Han-ZenX/GPSDO/docs/references/carsten-andrich-gnssdo/GNSSDO主板_渲染_揭开OCXO罩_v2.jpg

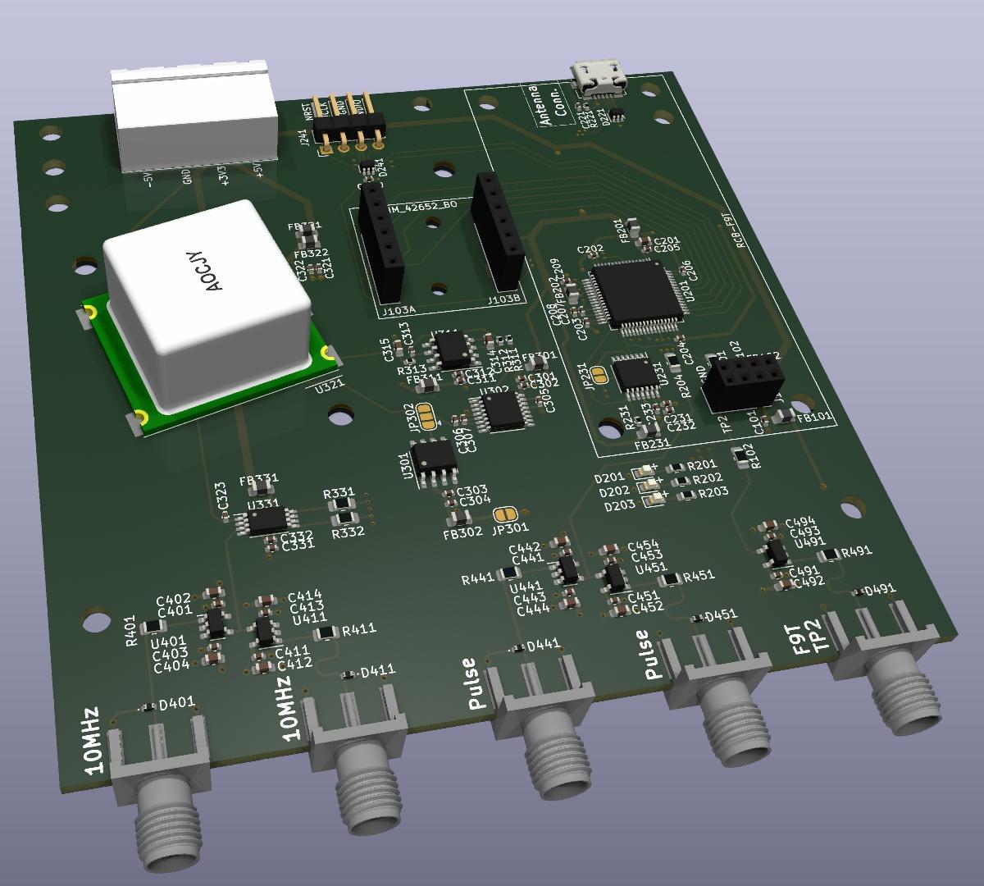
docs/references/carsten-andrich-gnssdo/GNSSDO主板_渲染_揭开OCXO罩_v2.jpg
