Han-ZenX/GPSDO/docs/references/carsten-andrich-gnssdo/GNSSDO主板_渲染_整板_v2.jpg

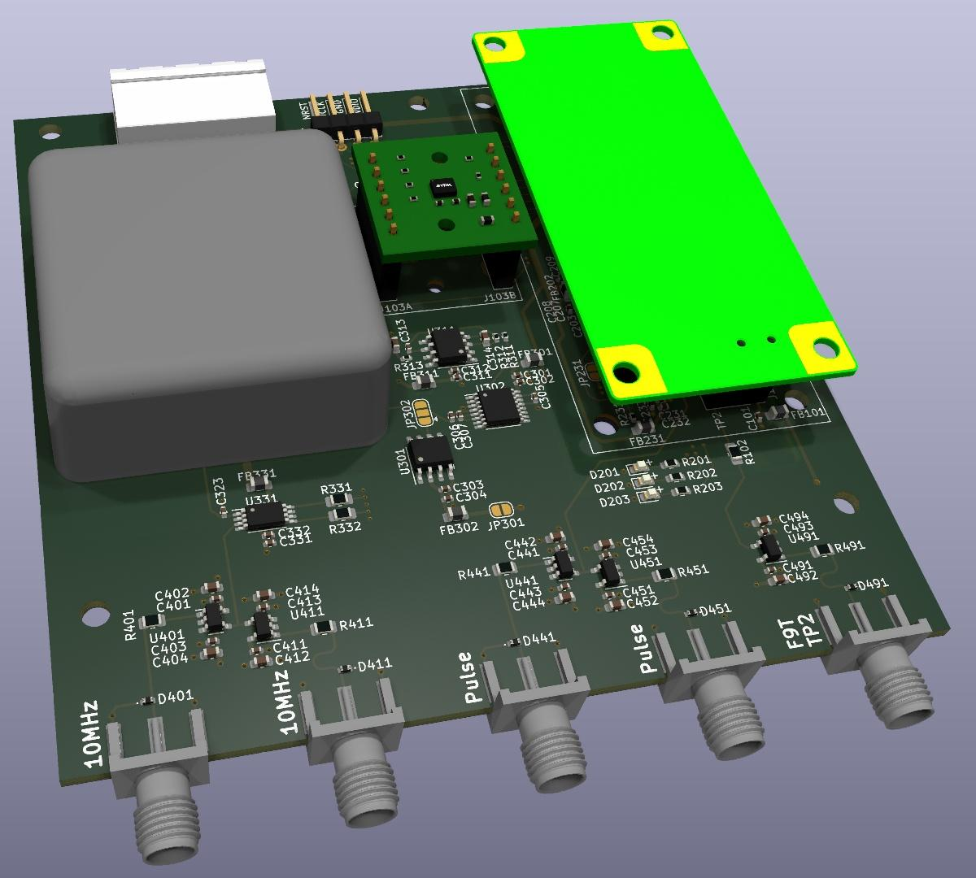
docs/references/carsten-andrich-gnssdo/GNSSDO主板_渲染_整板_v2.jpg
