Han-ZenX/GPSDO/docs/references/carsten-andrich-gnssdo/TDC7200测试板_实物_2022-08-28.jpg

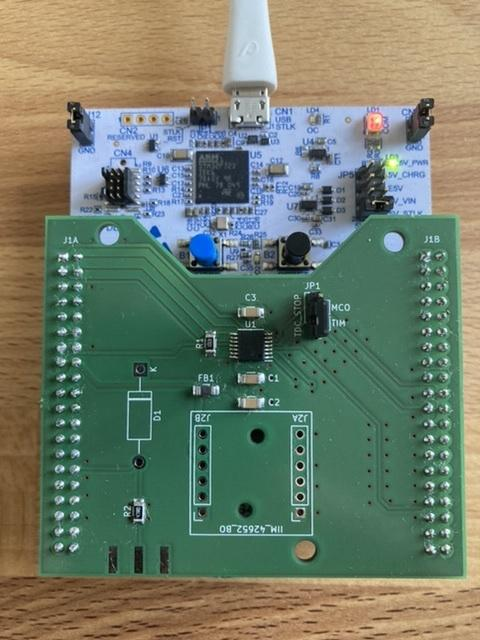
docs/references/carsten-andrich-gnssdo/TDC7200测试板_实物_2022-08-28.jpg
