Han-ZenX/GPSDO/hardware/schematic/v1.0/GPSDO_Rev1.0/GPSDO_Rev1.0.kicad_pcb

## KiCad design KiCad/steg_2.kicad_sch

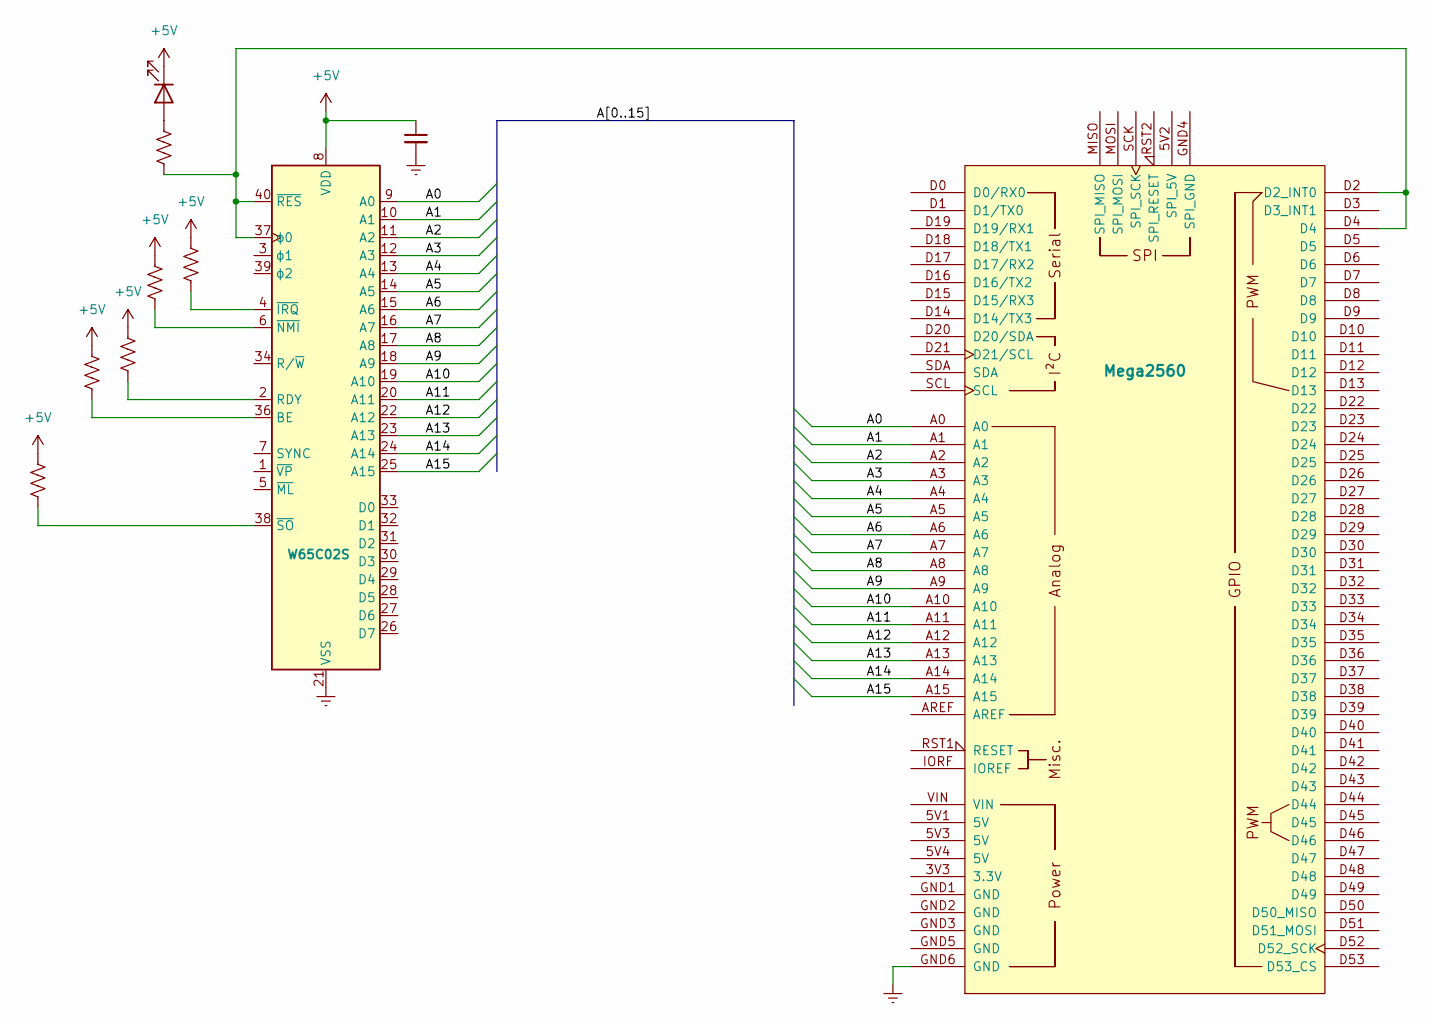
[picture p33: schematic steg_2.kicad_sch]

Parts:
A6: Mega2560; Arduino_Mega2560_R3_Shield
C2: 100nF
D2: LED
R29, R30, R31, R32, R33: (no value)
R34: 220
U12: W65C02S; DIP-40_W15.24mm

Connections:
+5V: C2.1, D2.1 (K), R29.1, R30.1, R31.1, R32.1, R33.1, U12.8 (VDD)
A0: A6.A0, U12.9 (A0)
A1: A6.A1, U12.10 (A1)
A2: A6.A2, U12.11 (A2)
A3: A6.A3, U12.12 (A3)
A4: A6.A4, U12.13 (A4)
A5: A6.A5, U12.14 (A5)
A6: A6.A6, U12.15 (A6)
A7: A6.A7, U12.16 (A7)
A8: A6.A8, U12.17 (A8)
A9: A6.A9, U12.18 (A9)
A10: A6.A10, U12.19 (A10)
A11: A6.A11, U12.20 (A11)
A12: A6.A12, U12.22 (A12)
A13: A6.A13, U12.23 (A13)
A14: A6.A14, U12.24 (A14)
A15: A6.A15, U12.25 (A15)
Earth: A6.GND6 (GND), C2.2, U12.21 (VSS)
unnamed: A6.D2 (D2_INT0), A6.D4, R34.2, U12.37 (ϕ0), U12.40 (~RES)
unnamed: D2.2 (A), R34.1
unnamed: R29.2, U12.38 (~SO)
unnamed: R30.2, U12.36 (BE)
unnamed: R31.2, U12.2 (RDY)
unnamed: R32.2, U12.6 (~NMI)
unnamed: R33.2, U12.4 (~IRQ)
