Han-ZenX/GPSDO/hardware/schematic/v1.0/GPSDO_Rev1.0/GPSDO_Rev1.0.kicad_pcb

## KiCad design KiCad/steg_4.kicad_sch

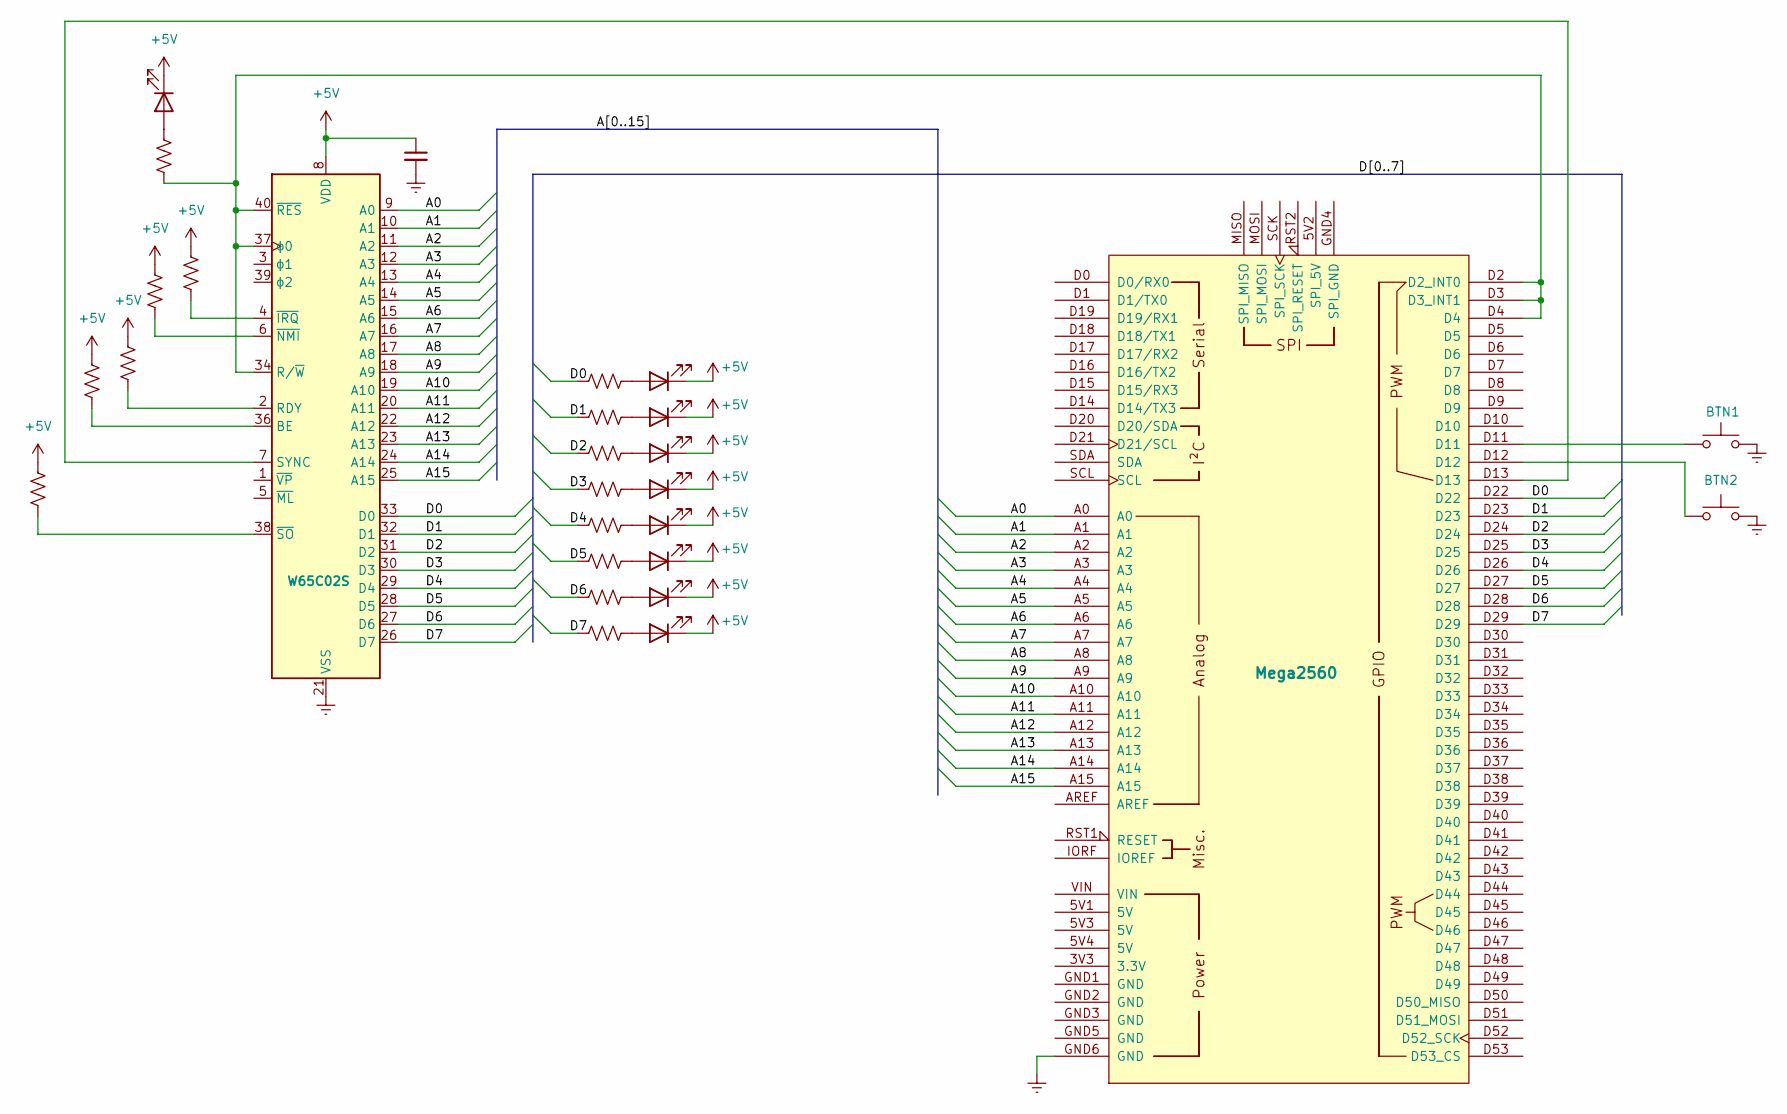
[picture p35: schematic steg_4.kicad_sch]

Parts:
A8: Mega2560; Arduino_Mega2560_R3_Shield
BTN1, BTN2: SW_Push
C4: 100nF
D12, D13, D14, D15, D16, D17, D18, D19, D20: LED
R49, R50, R51, R52, R54: (no value)
R53, R55, R56, R57, R58, R59, R60, R61, R62: 220
U14: W65C02S; DIP-40_W15.24mm

Connections:
+5V: C4.1, D12.1 (K), D13.1 (K), D14.1 (K), D15.1 (K), D16.1 (K), D17.1 (K), D18.1 (K), D19.1 (K), D20.1 (K), R49.1, R50.1, R51.1, R52.1, R54.1, U14.8 (VDD)
A0: A8.A0, U14.9 (A0)
A1: A8.A1, U14.10 (A1)
A2: A8.A2, U14.11 (A2)
A3: A8.A3, U14.12 (A3)
A4: A8.A4, U14.13 (A4)
A5: A8.A5, U14.14 (A5)
A6: A8.A6, U14.15 (A6)
A7: A8.A7, U14.16 (A7)
A8: A8.A8, U14.17 (A8)
A9: A8.A9, U14.18 (A9)
A10: A8.A10, U14.19 (A10)
A11: A8.A11, U14.20 (A11)
A12: A8.A12, U14.22 (A12)
A13: A8.A13, U14.23 (A13)
A14: A8.A14, U14.24 (A14)
A15: A8.A15, U14.25 (A15)
D0: A8.D22, R55.2, U14.33 (D0)
D1: A8.D23, R56.2, U14.32 (D1)
D2: A8.D24, R57.2, U14.31 (D2)
D3: A8.D25, R58.2, U14.30 (D3)
D4: A8.D26, R59.2, U14.29 (D4)
D5: A8.D27, R60.2, U14.28 (D5)
D6: A8.D28, R61.2, U14.27 (D6)
D7: A8.D29, R62.2, U14.26 (D7)
Earth: A8.GND6 (GND), BTN1.2, BTN2.2, C4.2, U14.21 (VSS)
unnamed: A8.D2 (D2_INT0), A8.D3 (D3_INT1), A8.D4, R53.2, U14.34 (R/~W), U14.37 (ϕ0), U14.40 (~RES)
unnamed: A8.D11, BTN1.1
unnamed: A8.D12, BTN2.1
unnamed: A8.D13, U14.7 (SYNC)
unnamed: D12.2 (A), R53.1
unnamed: D13.2 (A), R55.1
unnamed: D14.2 (A), R56.1
unnamed: D15.2 (A), R57.1
unnamed: D16.2 (A), R58.1
unnamed: D17.2 (A), R59.1
unnamed: D18.2 (A), R60.1
unnamed: D19.2 (A), R61.1
unnamed: D20.2 (A), R62.1
unnamed: R49.2, U14.38 (~SO)
unnamed: R50.2, U14.36 (BE)
unnamed: R51.2, U14.2 (RDY)
unnamed: R52.2, U14.6 (~NMI)
unnamed: R54.2, U14.4 (~IRQ)
