Han-ZenX/GPSDO/hardware/schematic/v1.0/GPSDO_Rev1.0/GPSDO_Rev1.0.kicad_pcb

## KiCad design KiCad/steg_5.kicad_sch

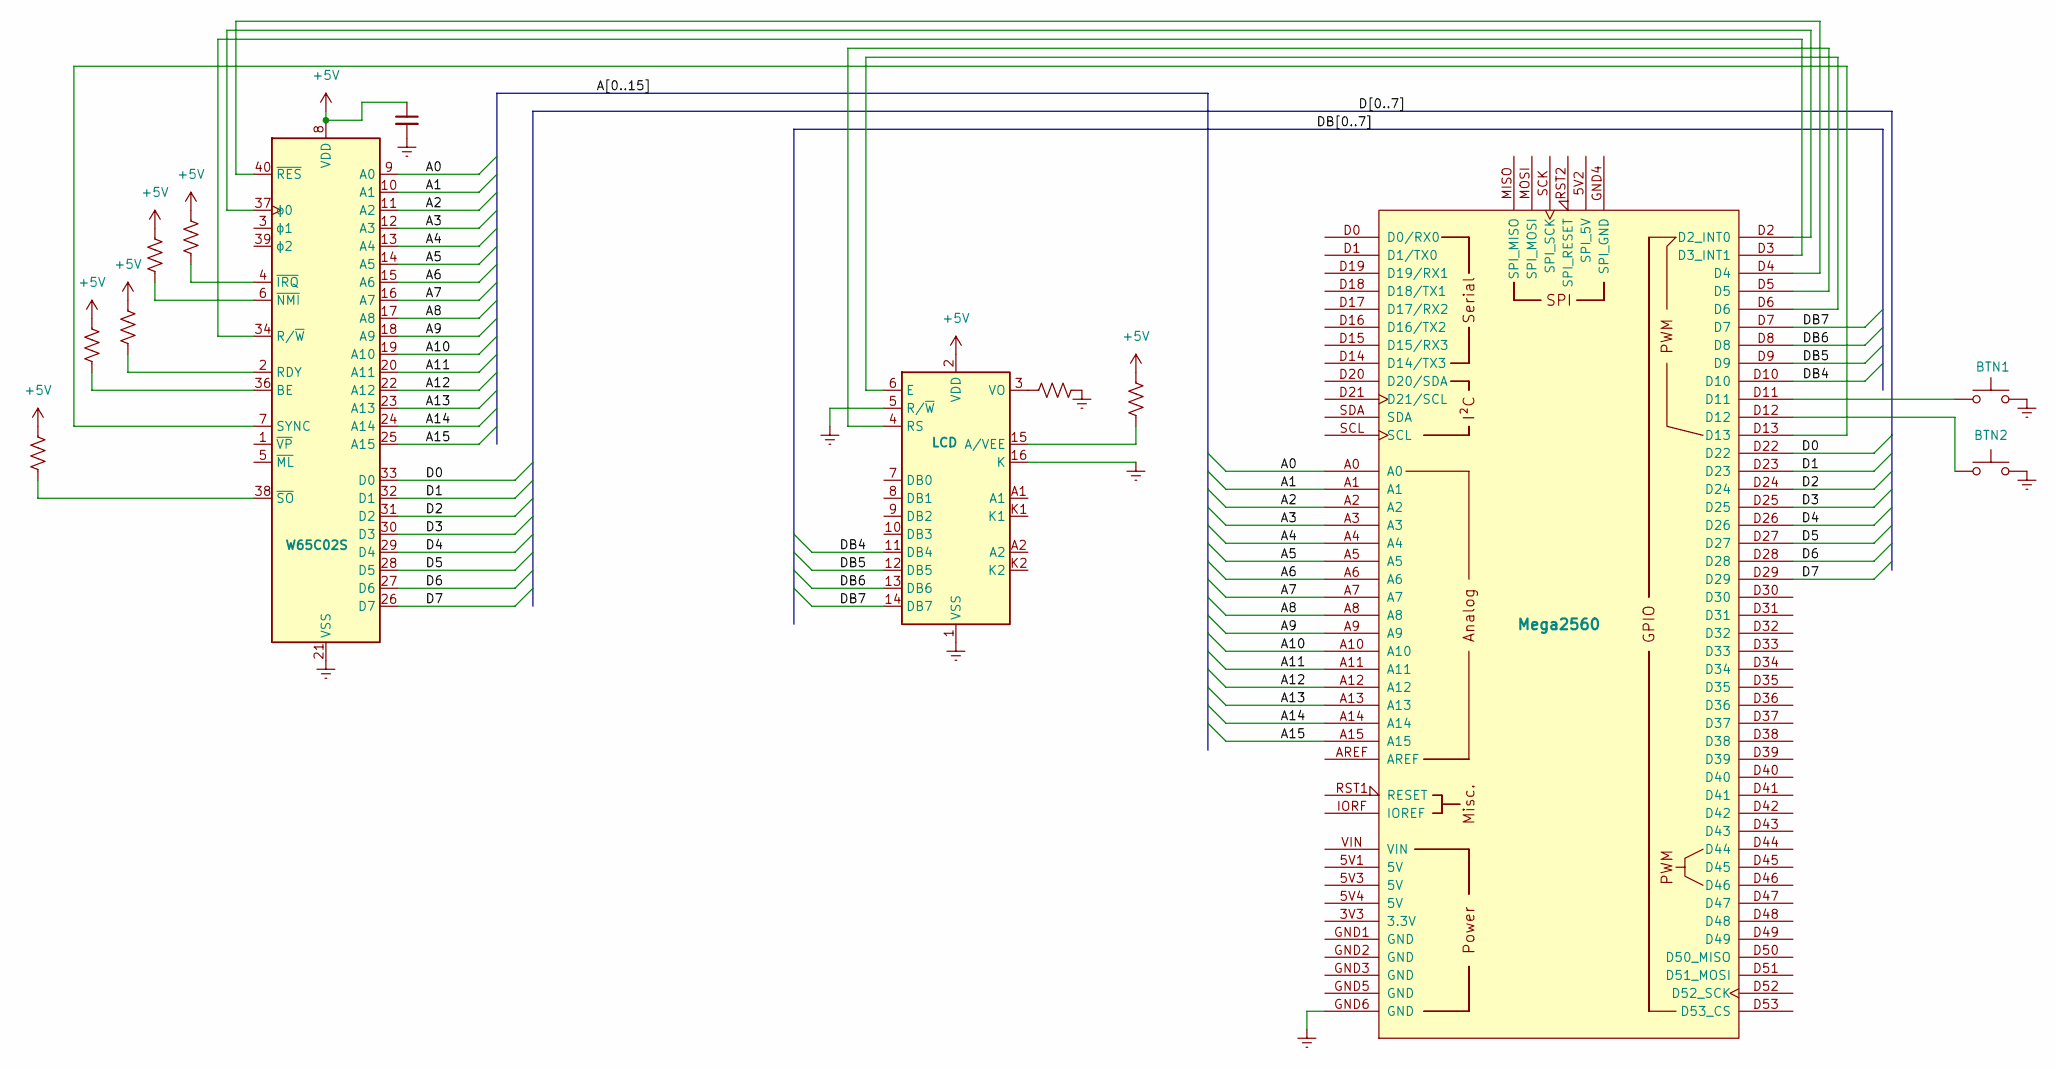
[picture p36: schematic steg_5.kicad_sch]

Parts:
A3: Mega2560; Arduino_Mega2560_R3_Shield
BTN1, BTN2: SW_Push
C5: 100nF
R15, R16, R17, R18, R19, R20, R21: (no value)
U7: W65C02S; DIP-40_W15.24mm
U8: LCD; LCD-016N002L

Connections:
+5V: C5.1, R15.1, R16.1, R17.1, R18.1, R19.1, R21.1, U7.8 (VDD), U8.2 (VDD)
A0: A3.A0, U7.9 (A0)
A1: A3.A1, U7.10 (A1)
A2: A3.A2, U7.11 (A2)
A3: A3.A3, U7.12 (A3)
A4: A3.A4, U7.13 (A4)
A5: A3.A5, U7.14 (A5)
A6: A3.A6, U7.15 (A6)
A7: A3.A7, U7.16 (A7)
A8: A3.A8, U7.17 (A8)
A9: A3.A9, U7.18 (A9)
A10: A3.A10, U7.19 (A10)
A11: A3.A11, U7.20 (A11)
A12: A3.A12, U7.22 (A12)
A13: A3.A13, U7.23 (A13)
A14: A3.A14, U7.24 (A14)
A15: A3.A15, U7.25 (A15)
D0: A3.D22, U7.33 (D0)
D1: A3.D23, U7.32 (D1)
D2: A3.D24, U7.31 (D2)
D3: A3.D25, U7.30 (D3)
D4: A3.D26, U7.29 (D4)
D5: A3.D27, U7.28 (D5)
D6: A3.D28, U7.27 (D6)
D7: A3.D29, U7.26 (D7)
DB4: A3.D10, U8.11 (DB4)
DB5: A3.D9, U8.12 (DB5)
DB6: A3.D8, U8.13 (DB6)
DB7: A3.D7, U8.14 (DB7)
Earth: A3.GND6 (GND), BTN1.2, BTN2.2, C5.2, R20.2, U7.21 (VSS), U8.1 (VSS), U8.5 (R/~W), U8.16 (K)
unnamed: A3.D2 (D2_INT0), U7.37 (ϕ0)
unnamed: A3.D3 (D3_INT1), U7.34 (R/~W)
unnamed: A3.D4, U7.40 (~RES)
unnamed: A3.D5, U8.4 (RS)
unnamed: A3.D6, U8.6 (E)
unnamed: A3.D11, BTN1.1
unnamed: A3.D12, BTN2.1
unnamed: A3.D13, U7.7 (SYNC)
unnamed: R15.2, U7.38 (~SO)
unnamed: R16.2, U7.36 (BE)
unnamed: R17.2, U7.2 (RDY)
unnamed: R18.2, U7.6 (~NMI)
unnamed: R19.2, U7.4 (~IRQ)
unnamed: R20.1, U8.3 (VO)
unnamed: R21.2, U8.15 (A/VEE)
