Han-ZenX/GPSDO/hardware/schematic/v1.0/GPSDO_Rev1.0/GPSDO_Rev1.0.kicad_pcb

## KiCad design KiCad/steg_6.kicad_sch

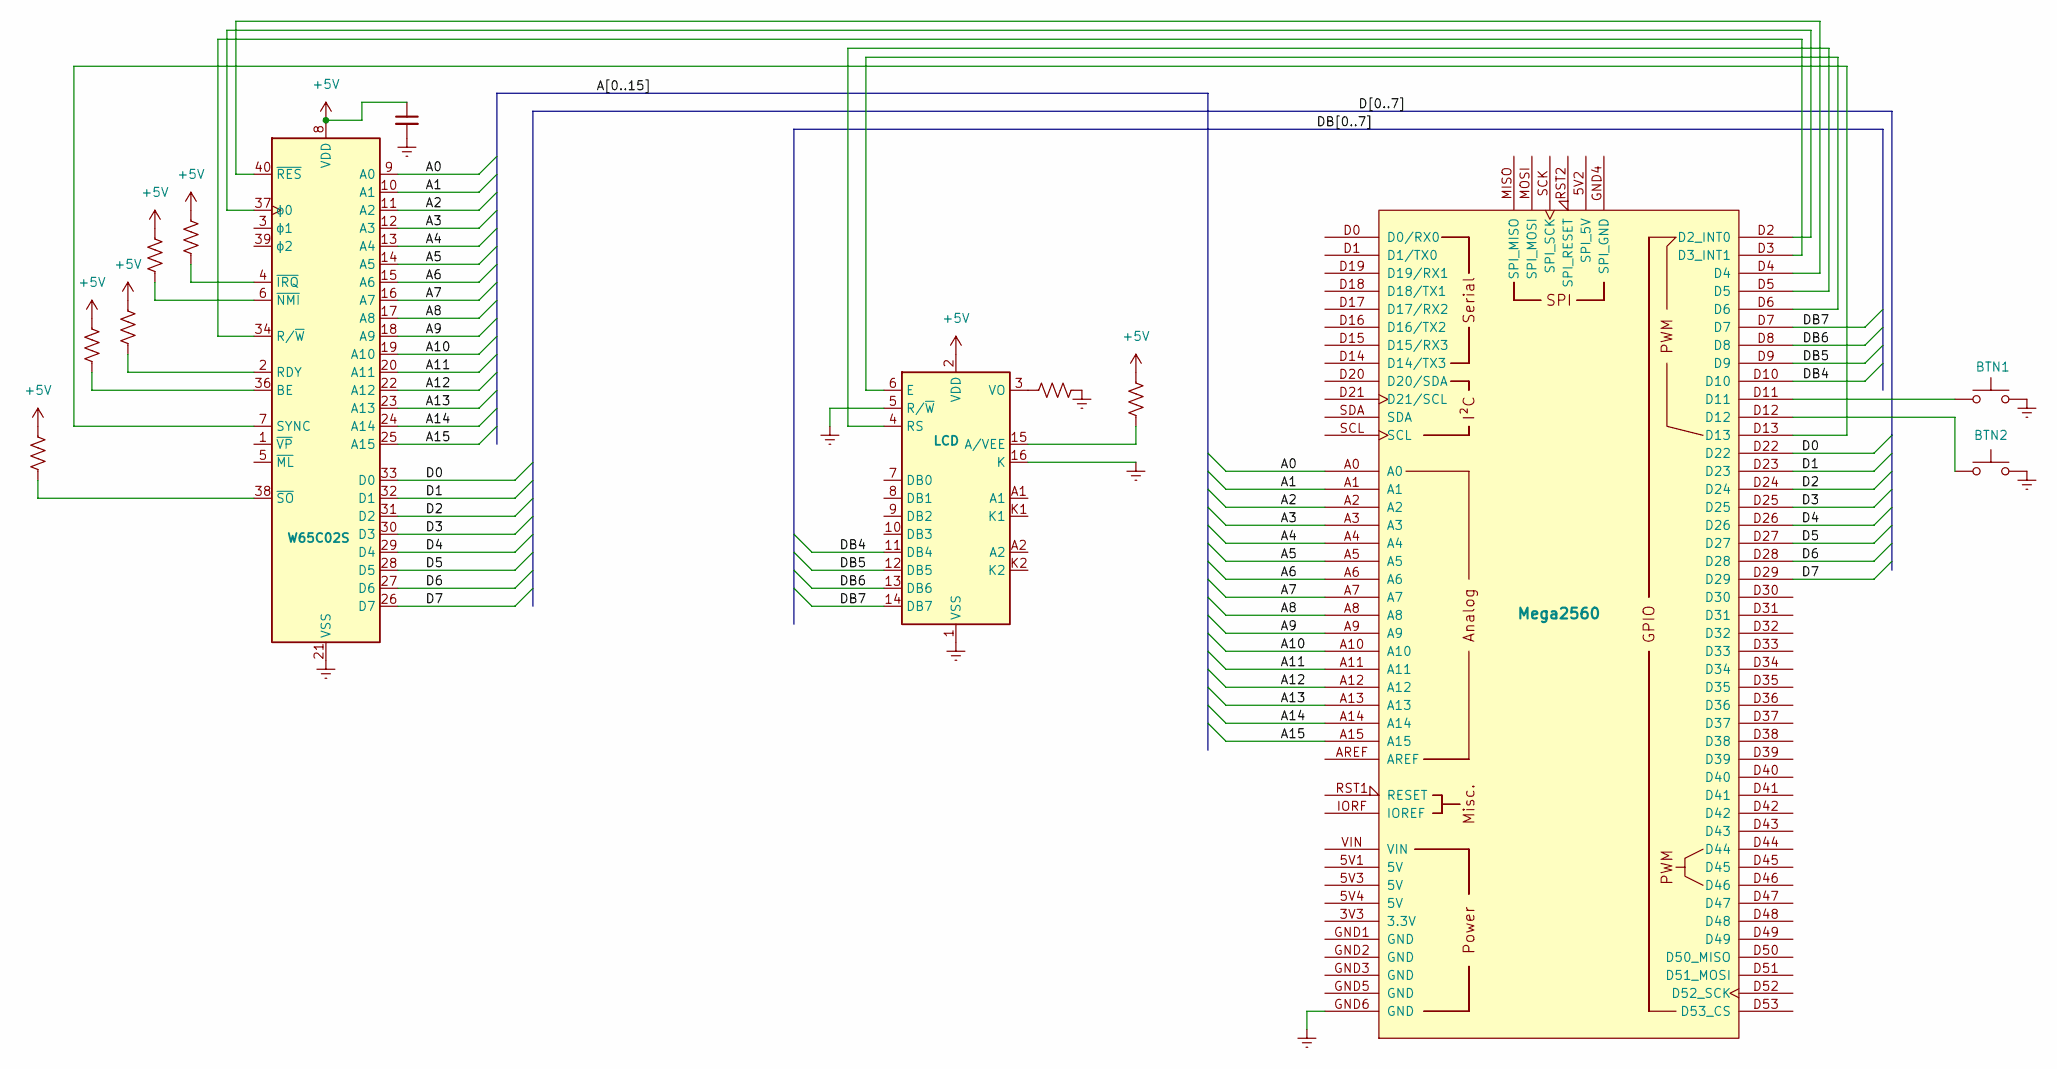
[picture p37: schematic steg_6.kicad_sch]

Parts:
A2: Mega2560; Arduino_Mega2560_R3_Shield
BTN1, BTN2: SW_Push
C6: 100nF
R8, R9, R10, R11, R12, R13, R14: (no value)
U5: W65C02S; DIP-40_W15.24mm
U6: LCD; LCD-016N002L

Connections:
+5V: C6.1, R8.1, R9.1, R10.1, R11.1, R12.1, R14.1, U5.8 (VDD), U6.2 (VDD)
A0: A2.A0, U5.9 (A0)
A1: A2.A1, U5.10 (A1)
A2: A2.A2, U5.11 (A2)
A3: A2.A3, U5.12 (A3)
A4: A2.A4, U5.13 (A4)
A5: A2.A5, U5.14 (A5)
A6: A2.A6, U5.15 (A6)
A7: A2.A7, U5.16 (A7)
A8: A2.A8, U5.17 (A8)
A9: A2.A9, U5.18 (A9)
A10: A2.A10, U5.19 (A10)
A11: A2.A11, U5.20 (A11)
A12: A2.A12, U5.22 (A12)
A13: A2.A13, U5.23 (A13)
A14: A2.A14, U5.24 (A14)
A15: A2.A15, U5.25 (A15)
D0: A2.D22, U5.33 (D0)
D1: A2.D23, U5.32 (D1)
D2: A2.D24, U5.31 (D2)
D3: A2.D25, U5.30 (D3)
D4: A2.D26, U5.29 (D4)
D5: A2.D27, U5.28 (D5)
D6: A2.D28, U5.27 (D6)
D7: A2.D29, U5.26 (D7)
DB4: A2.D10, U6.11 (DB4)
DB5: A2.D9, U6.12 (DB5)
DB6: A2.D8, U6.13 (DB6)
DB7: A2.D7, U6.14 (DB7)
Earth: A2.GND6 (GND), BTN1.2, BTN2.2, C6.2, R13.2, U5.21 (VSS), U6.1 (VSS), U6.5 (R/~W), U6.16 (K)
unnamed: A2.D2 (D2_INT0), U5.37 (ϕ0)
unnamed: A2.D3 (D3_INT1), U5.34 (R/~W)
unnamed: A2.D4, U5.40 (~RES)
unnamed: A2.D5, U6.4 (RS)
unnamed: A2.D6, U6.6 (E)
unnamed: A2.D11, BTN1.1
unnamed: A2.D12, BTN2.1
unnamed: A2.D13, U5.7 (SYNC)
unnamed: R8.2, U5.38 (~SO)
unnamed: R9.2, U5.36 (BE)
unnamed: R10.2, U5.2 (RDY)
unnamed: R11.2, U5.6 (~NMI)
unnamed: R12.2, U5.4 (~IRQ)
unnamed: R13.1, U6.3 (VO)
unnamed: R14.2, U6.15 (A/VEE)
