Han-ZenX/GPSDO/hardware/schematic/v1.0/GPSDO_Rev1.0/GPSDO_Rev1.0.kicad_pcb

## KiCad design KiCad/steg_11.kicad_sch

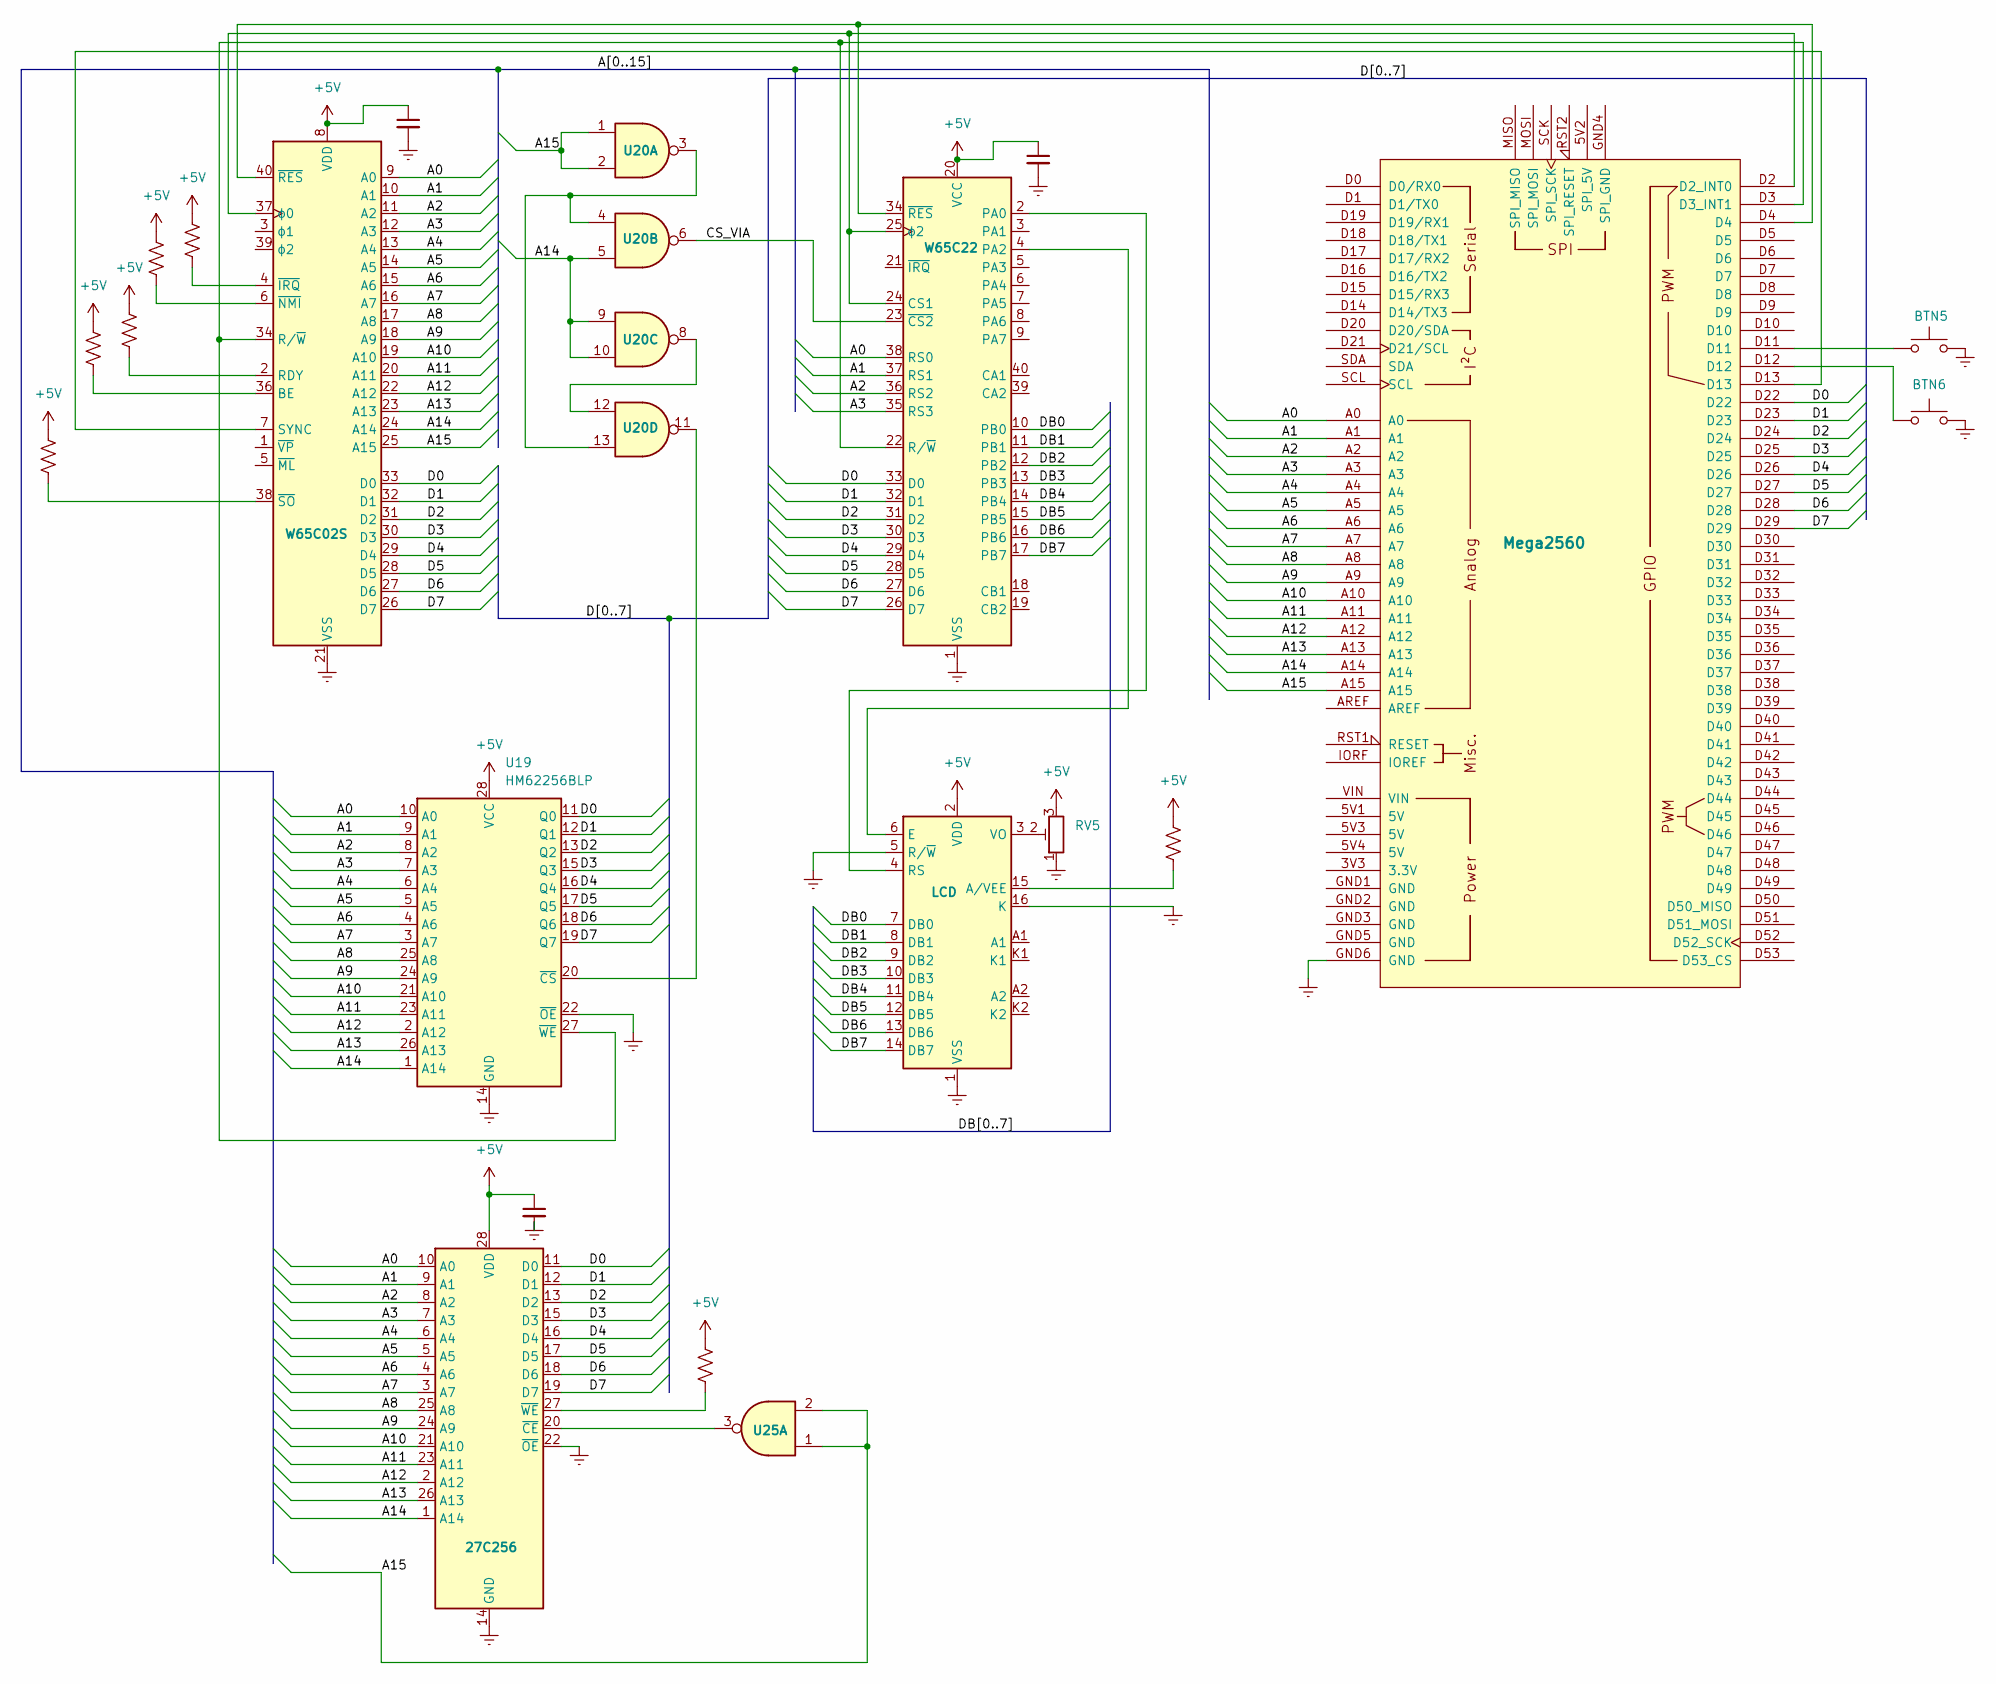
[picture p41: schematic steg_11.kicad_sch]

Parts:
A10: Mega2560; Arduino_Mega2560_R3_Shield
BTN5, BTN6: SW_Push
C12, C13, C14: 100nF
R25, R26, R27, R28, R63, R65: (no value)
R64: 220
RV5: R_Potentiometer_Trim
U18: W65C02S; DIP-40_W15.24mm
U19: HM62256BLP; DIP-28_W15.24mm
U20, U25: 74HC00
U21: W65C22; DIP-40_W15.24mm
U22: LCD; LCD-016N002L
U23: 27C256; DIP-28_W15.24mm

Connections:
+5V: C12.1, C13.1, C14.1, R25.1, R26.1, R27.1, R28.1, R63.1, R64.1, R65.1, RV5.3, U18.8 (VDD), U19.28 (VCC), U21.20 (VCC), U22.2 (VDD), U23.28 (VDD)
A0: A10.A0, U18.9 (A0), U19.10 (A0), U21.38 (RS0), U23.10 (A0)
A1: A10.A1, U18.10 (A1), U19.9 (A1), U21.37 (RS1), U23.9 (A1)
A2: A10.A2, U18.11 (A2), U19.8 (A2), U21.36 (RS2), U23.8 (A2)
A3: A10.A3, U18.12 (A3), U19.7 (A3), U21.35 (RS3), U23.7 (A3)
A4: A10.A4, U18.13 (A4), U19.6 (A4), U23.6 (A4)
A5: A10.A5, U18.14 (A5), U19.5 (A5), U23.5 (A5)
A6: A10.A6, U18.15 (A6), U19.4 (A6), U23.4 (A6)
A7: A10.A7, U18.16 (A7), U19.3 (A7), U23.3 (A7)
A8: A10.A8, U18.17 (A8), U19.25 (A8), U23.25 (A8)
A9: A10.A9, U18.18 (A9), U19.24 (A9), U23.24 (A9)
A10: A10.A10, U18.19 (A10), U19.21 (A10), U23.21 (A10)
A11: A10.A11, U18.20 (A11), U19.23 (A11), U23.23 (A11)
A12: A10.A12, U18.22 (A12), U19.2 (A12), U23.2 (A12)
A13: A10.A13, U18.23 (A13), U19.26 (A13), U23.26 (A13)
A14: A10.A14, U18.24 (A14), U19.1 (A14), U20.5, U20.9, U20.10, U23.1 (A14)
A15: A10.A15, U18.25 (A15), U20.1, U20.2, U25.1, U25.2
CS_VIA: U20.6, U21.23 (~CS2)
D0: A10.D22, U18.33 (D0), U19.11 (Q0), U21.33 (D0), U23.11 (D0)
D1: A10.D23, U18.32 (D1), U19.12 (Q1), U21.32 (D1), U23.12 (D1)
D2: A10.D24, U18.31 (D2), U19.13 (Q2), U21.31 (D2), U23.13 (D2)
D3: A10.D25, U18.30 (D3), U19.15 (Q3), U21.30 (D3), U23.15 (D3)
D4: A10.D26, U18.29 (D4), U19.16 (Q4), U21.29 (D4), U23.16 (D4)
D5: A10.D27, U18.28 (D5), U19.17 (Q5), U21.28 (D5), U23.17 (D5)
D6: A10.D28, U18.27 (D6), U19.18 (Q6), U21.27 (D6), U23.18 (D6)
D7: A10.D29, U18.26 (D7), U19.19 (Q7), U21.26 (D7), U23.19 (D7)
DB0: U21.10 (PB0), U22.7 (DB0)
DB1: U21.11 (PB1), U22.8 (DB1)
DB2: U21.12 (PB2), U22.9 (DB2)
DB3: U21.13 (PB3), U22.10 (DB3)
DB4: U21.14 (PB4), U22.11 (DB4)
DB5: U21.15 (PB5), U22.12 (DB5)
DB6: U21.16 (PB6), U22.13 (DB6)
DB7: U21.17 (PB7), U22.14 (DB7)
Earth: A10.GND6 (GND), BTN5.2, BTN6.2, C12.2, C13.2, C14.2, RV5.1, U18.21 (VSS), U19.14 (GND), U19.22 (~OE), U21.1 (VSS), U22.1 (VSS), U22.5 (R/~W), U22.16 (K), U23.14 (GND), U23.22 (~OE)
unnamed: A10.D2 (D2_INT0), U18.37 (ϕ0), U21.24 (CS1), U21.25 (ϕ2)
unnamed: A10.D3 (D3_INT1), U18.34 (R/~W), U19.27 (~WE), U21.22 (R/~W)
unnamed: A10.D4, U18.40 (~RES), U21.34 (~RES)
unnamed: A10.D11, BTN5.1
unnamed: A10.D12, BTN6.1
unnamed: A10.D13, U18.7 (SYNC)
unnamed: R25.2, U18.38 (~SO)
unnamed: R26.2, U18.36 (BE)
unnamed: R27.2, U18.2 (RDY)
unnamed: R28.2, U18.6 (~NMI)
unnamed: R63.2, U18.4 (~IRQ)
unnamed: R64.2, U22.15 (A/VEE)
unnamed: R65.2, U23.27 (~WE)
unnamed: RV5.2, U22.3 (VO)
unnamed: U19.20 (~CS), U20.11
unnamed: U20.8, U20.12
unnamed: U20.3, U20.4, U20.13
unnamed: U21.2 (PA0), U22.4 (RS)
unnamed: U21.4 (PA2), U22.6 (E)
unnamed: U23.20 (~CE), U25.3
