Han-ZenX/GPSDO/hardware/schematic/v1.0/GPSDO_Rev1.0/GPSDO_Rev1.0.kicad_pcb

## KiCad design KiCad/6502.smutje.se.steg-6/6502.smutje.se.kicad_sch

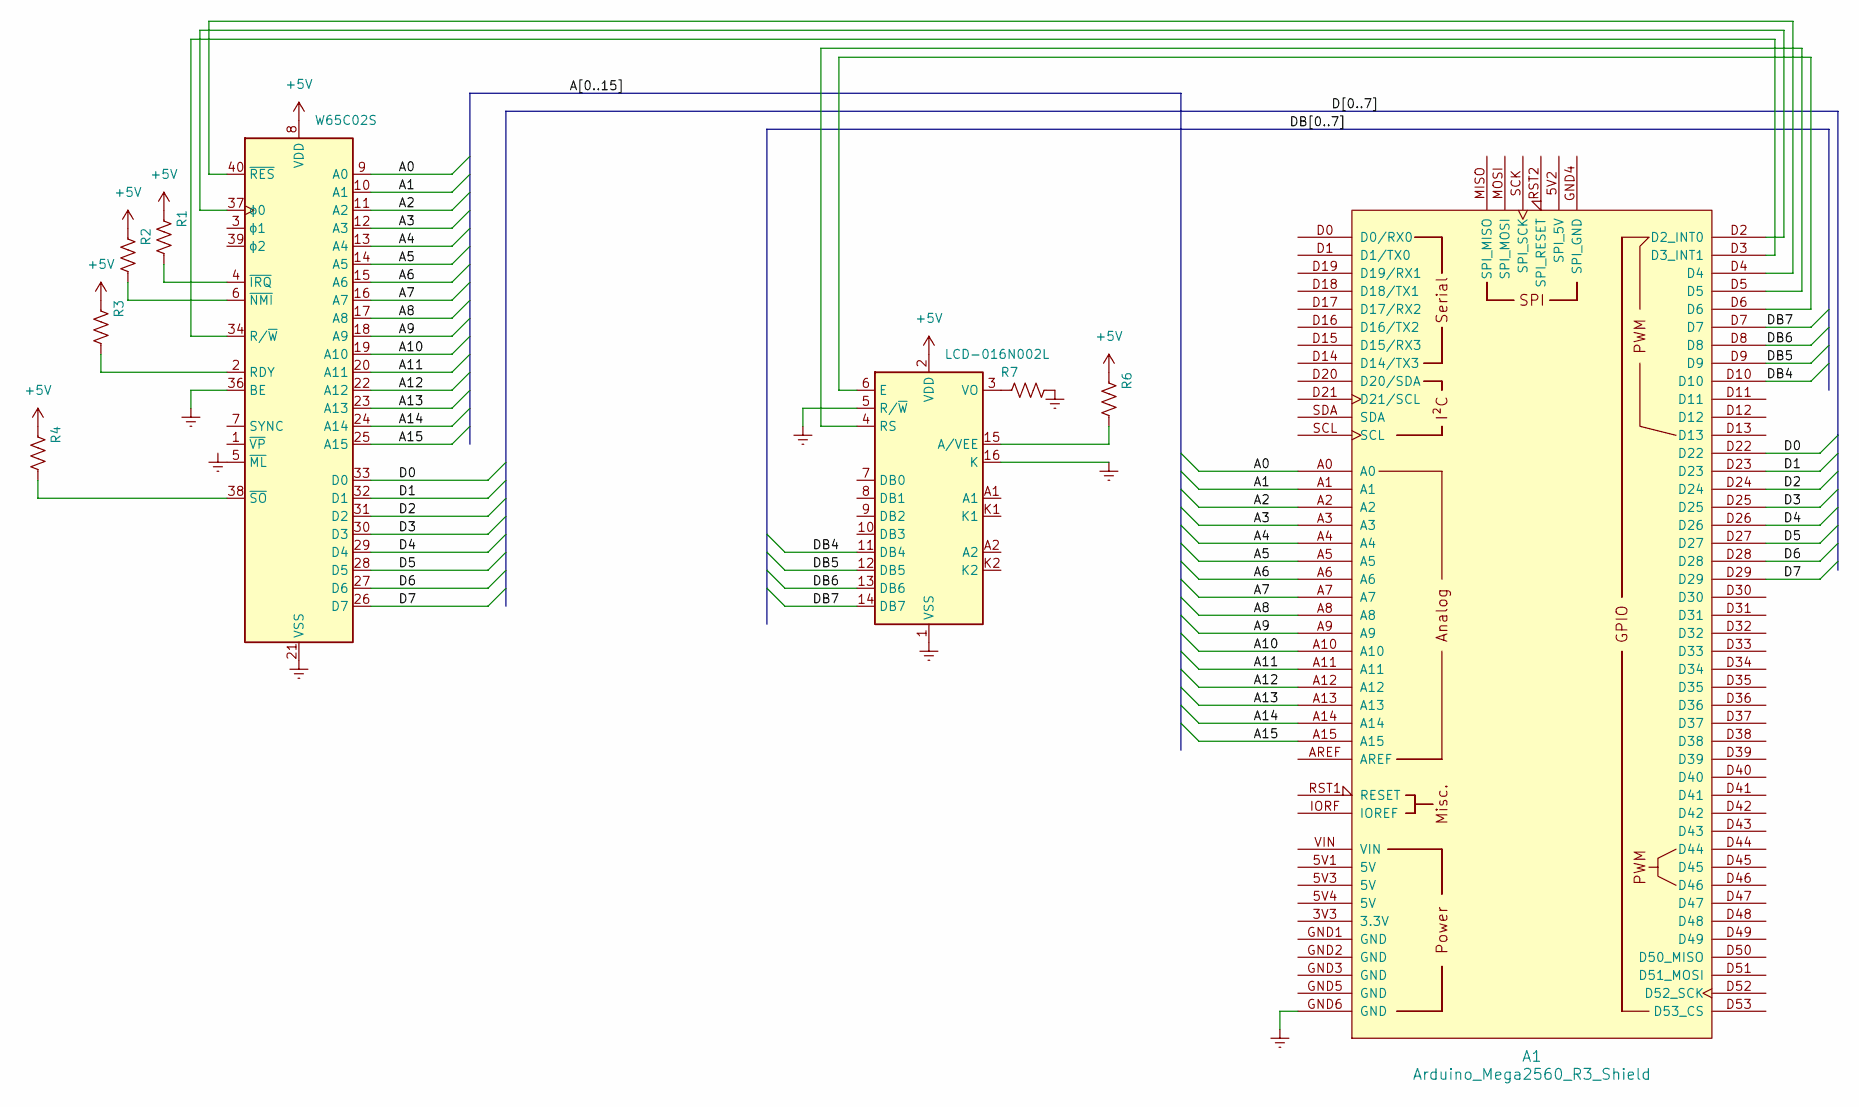
[picture p42: schematic 6502.smutje.se.kicad_sch]

Parts:
A1: Arduino_Mega2560_R3_Shield
R1, R2, R3, R4, R6, R7: (no value)
U1: W65C02S; DIP-40_W15.24mm
U2: LCD-016N002L

Connections:
+5V: R1.1, R2.1, R3.1, R4.1, R6.1, U1.8 (VDD), U2.2 (VDD)
A0: A1.A0, U1.9 (A0)
A1: A1.A1, U1.10 (A1)
A2: A1.A2, U1.11 (A2)
A3: A1.A3, U1.12 (A3)
A4: A1.A4, U1.13 (A4)
A5: A1.A5, U1.14 (A5)
A6: A1.A6, U1.15 (A6)
A7: A1.A7, U1.16 (A7)
A8: A1.A8, U1.17 (A8)
A9: A1.A9, U1.18 (A9)
A10: A1.A10, U1.19 (A10)
A11: A1.A11, U1.20 (A11)
A12: A1.A12, U1.22 (A12)
A13: A1.A13, U1.23 (A13)
A14: A1.A14, U1.24 (A14)
A15: A1.A15, U1.25 (A15)
D0: A1.D22, U1.33 (D0)
D1: A1.D23, U1.32 (D1)
D2: A1.D24, U1.31 (D2)
D3: A1.D25, U1.30 (D3)
D4: A1.D26, U1.29 (D4)
D5: A1.D27, U1.28 (D5)
D6: A1.D28, U1.27 (D6)
D7: A1.D29, U1.26 (D7)
DB4: A1.D10, U2.11 (DB4)
DB5: A1.D9, U2.12 (DB5)
DB6: A1.D8, U2.13 (DB6)
DB7: A1.D7, U2.14 (DB7)
Earth: A1.GND6 (GND), R7.2, U1.21 (VSS), U1.36 (BE), U2.1 (VSS), U2.5 (R/~W), U2.16 (K)
unnamed: A1.D2 (D2_INT0), U1.37 (ϕ0)
unnamed: A1.D3 (D3_INT1), U1.34 (R/~W)
unnamed: A1.D4, U1.40 (~RES)
unnamed: A1.D5, U2.4 (RS)
unnamed: A1.D6, U2.6 (E)
unnamed: R1.2, U1.4 (~IRQ)
unnamed: R2.2, U1.6 (~NMI)
unnamed: R3.2, U1.2 (RDY)
unnamed: R4.2, U1.38 (~SO)
unnamed: R6.2, U2.15 (A/VEE)
unnamed: R7.1, U2.3 (VO)
